ETSA-USJ/curso-3d-printing/Piezas Imprimibles/PrusaMendel_IT2_Usj/metric-prusa-lme8uu/ybrac-t.stl

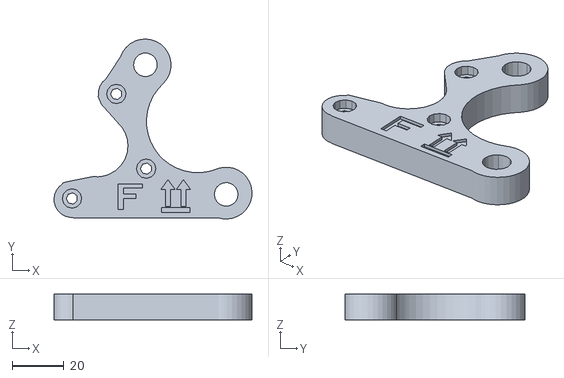
[picture p34: CAD file, 2014-04-24]
Piezas Imprimibles/PrusaMendel_IT2_Usj/metric-prusa-lme8uu/ybrac-t.stl
76.4 x 69.4 x 10.0
