ETSA-USJ/curso-3d-printing/Piezas Imprimibles/PrusaMendel_IT2_Usj/metric-prusa/printable-bushing-lm8uu.stl

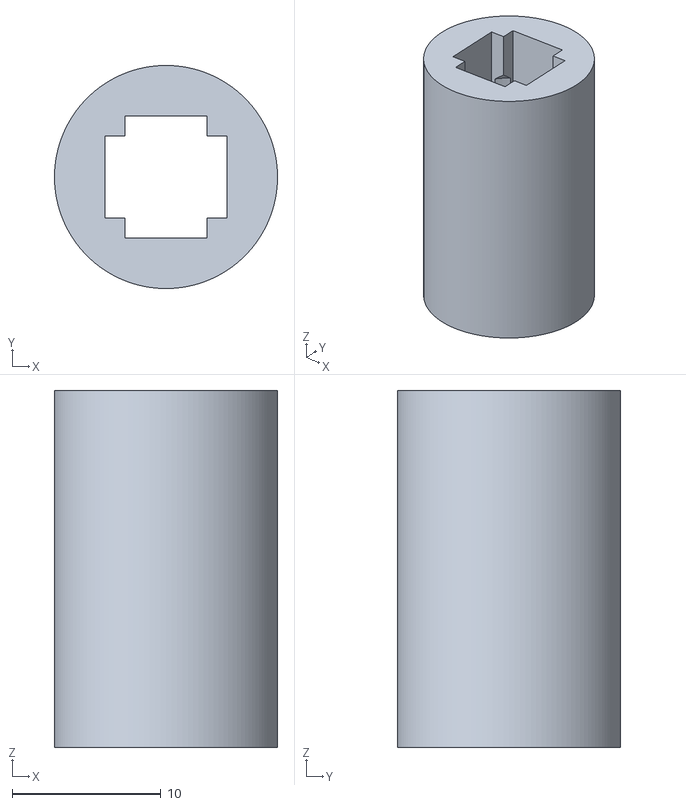
[picture p35: CAD file, 2014-04-24]
Piezas Imprimibles/PrusaMendel_IT2_Usj/metric-prusa/printable-bushing-lm8uu.stl
15.0 x 15.0 x 24.0
