ETSA-USJ/curso-3d-printing/Piezas Imprimibles/PrusaMendel_IT2_Usj/metric-prusa-lm8uu/frame-vertex.stl

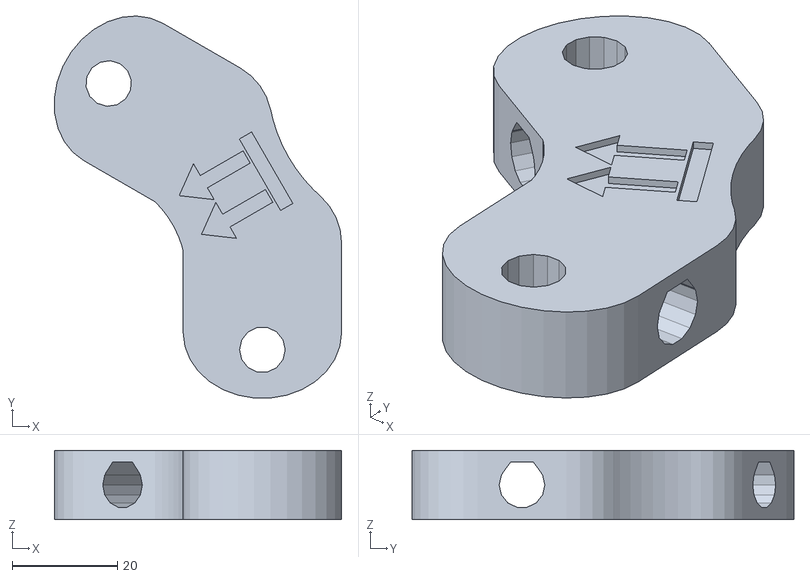
[picture p36: CAD file, 2014-04-24]
Piezas Imprimibles/PrusaMendel_IT2_Usj/metric-prusa-lm8uu/frame-vertex.stl
54.7 x 72.7 x 13.2
