ETSA-USJ/curso-3d-printing/Piezas Imprimibles/PrusaMendel_IT2_Usj/metric-prusa-lme8uu/frame-vertex-foot.stl

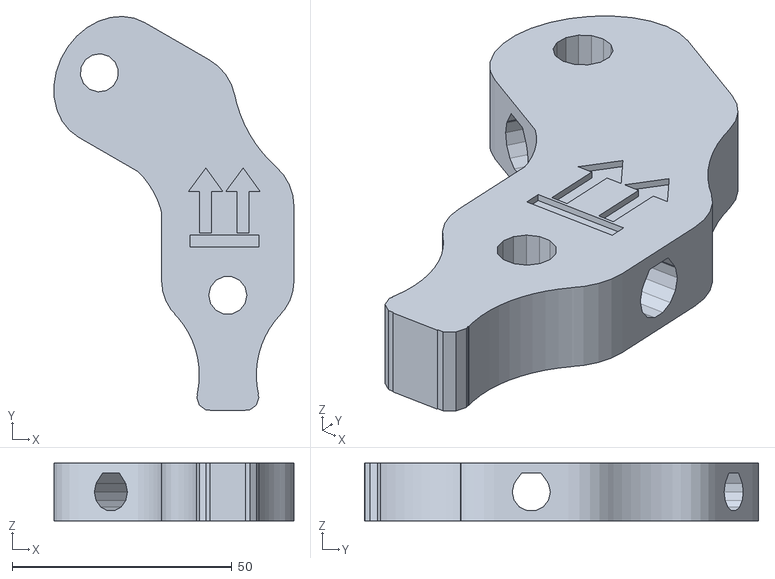
[picture p37: CAD file, 2014-04-24]
Piezas Imprimibles/PrusaMendel_IT2_Usj/metric-prusa-lme8uu/frame-vertex-foot.stl
54.7 x 89.8 x 13.2
