ETSA-USJ/curso-3d-printing/Piezas Imprimibles/PrusaMendel_IT2_Usj/metric-prusa-lm8uu/x-carriage.stl

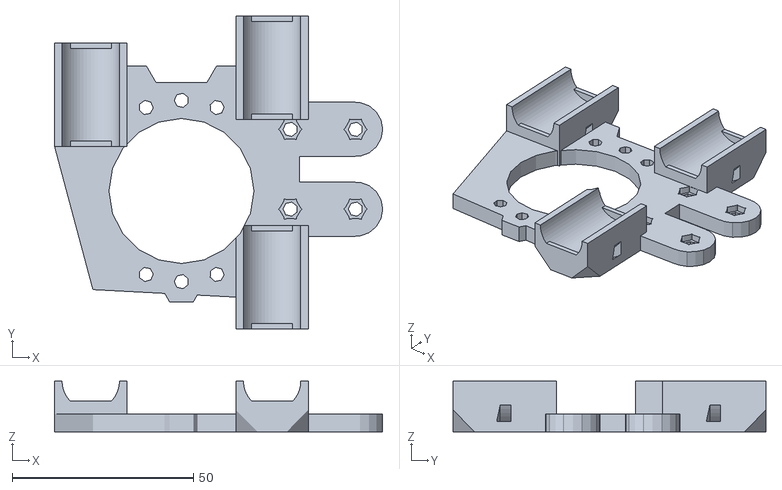
[picture p38: CAD file, 2014-04-24]
Piezas Imprimibles/PrusaMendel_IT2_Usj/metric-prusa-lm8uu/x-carriage.stl
90.6 x 86.3 x 14.0
