ETSA-USJ/curso-3d-printing/Piezas Imprimibles/PrusaMendel_IT2_Usj/metric-prusa-lme8uu/printable-bushing.stl

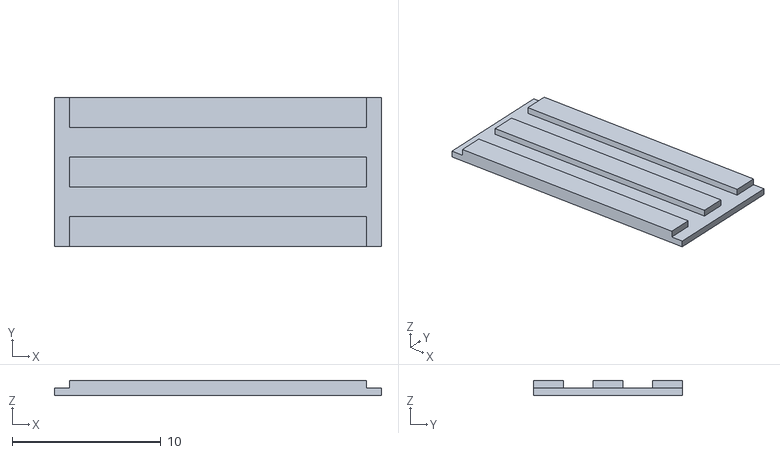
[picture p39: CAD file, 2014-04-24]
Piezas Imprimibles/PrusaMendel_IT2_Usj/metric-prusa-lme8uu/printable-bushing.stl
22.0 x 10.0 x 1.00
