ETSA-USJ/curso-3d-printing/Piezas Imprimibles/PrusaMendel_IT2_Usj/metric-prusa-lme8uu/x-end-motor.stl

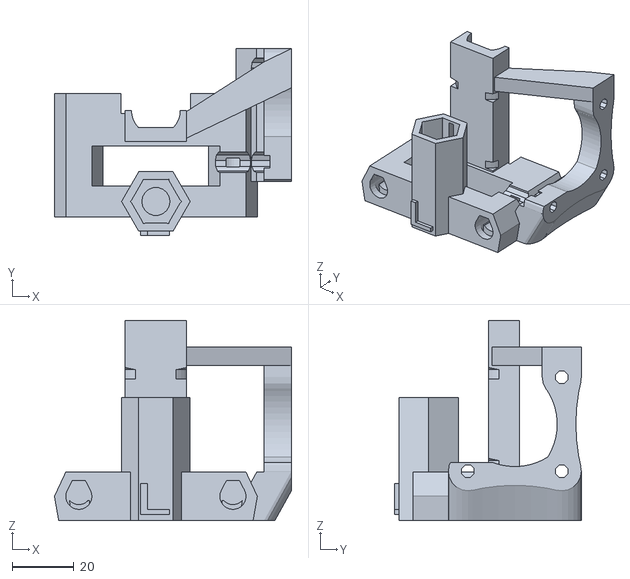
[picture p40: CAD file, 2014-04-24]
Piezas Imprimibles/PrusaMendel_IT2_Usj/metric-prusa-lme8uu/x-end-motor.stl
76.9 x 60.6 x 65.0
