ETSA-USJ/curso-3d-printing/Piezas Imprimibles/PrusaMendel_IT2_Usj/metric-prusa/rod-clamp.stl

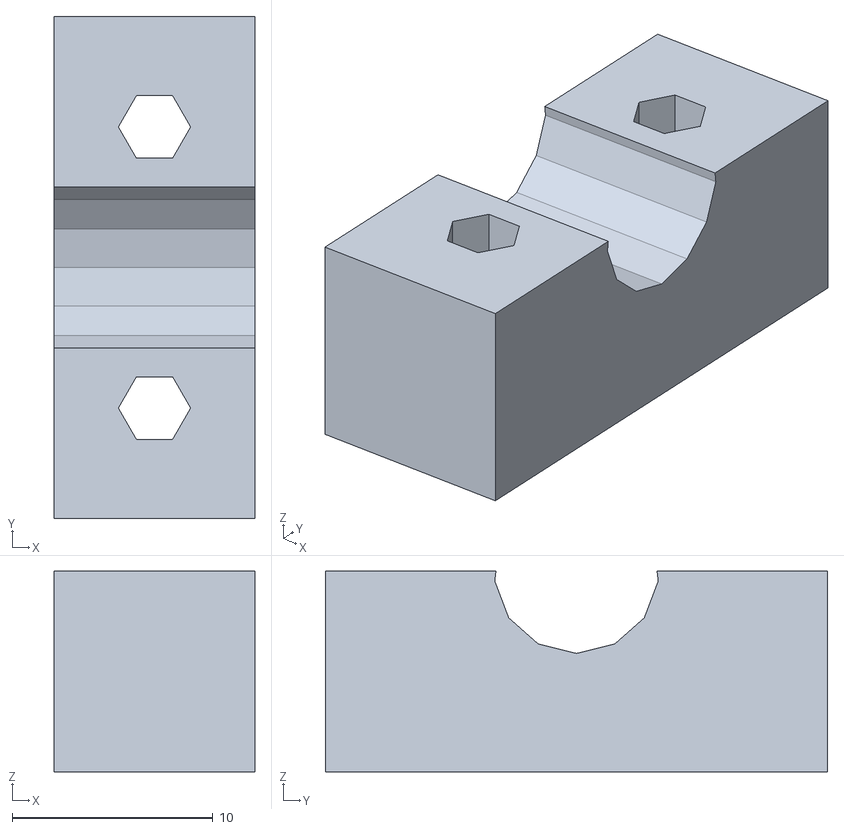
[picture p41: CAD file, 2014-04-24]
Piezas Imprimibles/PrusaMendel_IT2_Usj/metric-prusa/rod-clamp.stl
10.0 x 25.0 x 10.0
