ETSA-USJ/curso-3d-printing/Piezas Imprimibles/PrusaMendel_IT2_Usj/metric-prusa-lme8uu/endstop-holder.stl

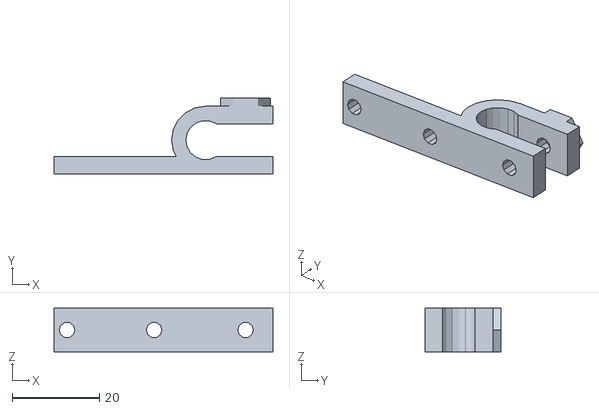
[picture p42: CAD file, 2014-04-24]
Piezas Imprimibles/PrusaMendel_IT2_Usj/metric-prusa-lme8uu/endstop-holder.stl
50.3 x 17.5 x 10.0
