ETSA-USJ/curso-3d-printing/Piezas Imprimibles/PrusaMendel_IT2_Usj/metric-prusa/mendel-plate-1.stl

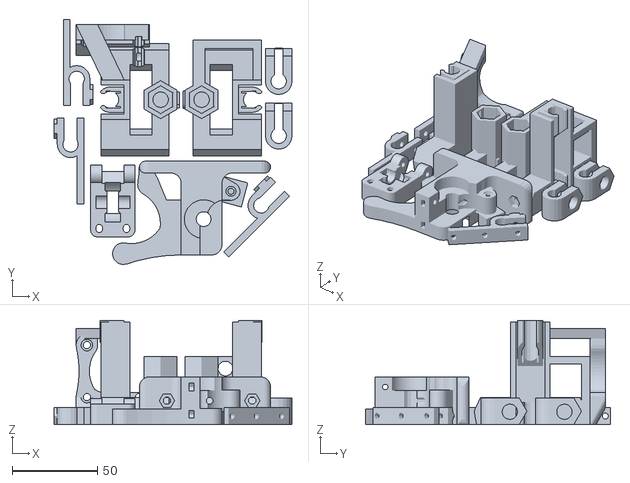
[picture p43: CAD file, 2014-04-24]
Piezas Imprimibles/PrusaMendel_IT2_Usj/metric-prusa/mendel-plate-1.stl
139.5 x 143.6 x 61.0
