ETSA-USJ/curso-3d-printing/Piezas Imprimibles/PrusaMendel_IT2_Usj/metric-prusa-lm8uu/sanguinololu-holder.stl

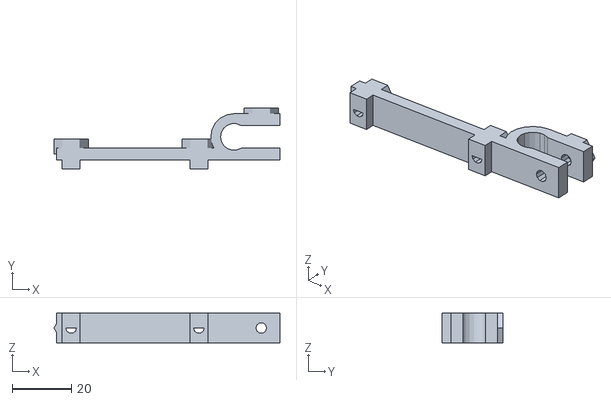
[picture p44: CAD file, 2014-04-24]
Piezas Imprimibles/PrusaMendel_IT2_Usj/metric-prusa-lm8uu/sanguinololu-holder.stl
76.1 x 20.5 x 10.0
