ETSA-USJ/curso-3d-printing/Piezas Imprimibles/PrusaMendel_IT2_Usj/metric-prusa/mendel-plate-2.stl

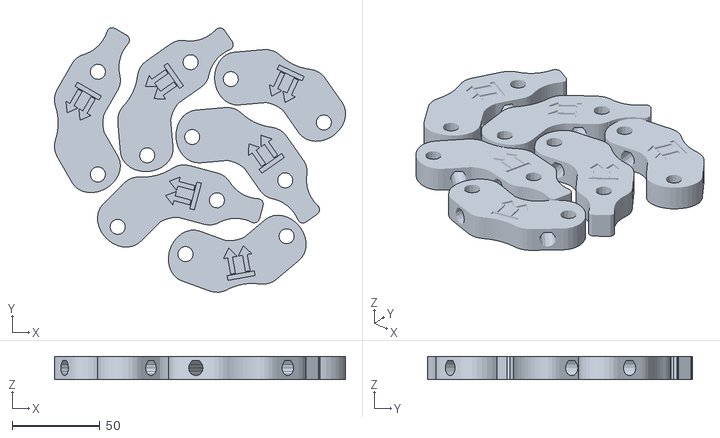
[picture p47: CAD file, 2014-04-24]
Piezas Imprimibles/PrusaMendel_IT2_Usj/metric-prusa/mendel-plate-2.stl
165.8 x 150.8 x 13.2
