ETSA-USJ/curso-3d-printing/Piezas Imprimibles/PrusaMendel_IT2_Usj/metric-prusa-lm8uu/bar-clamp.stl

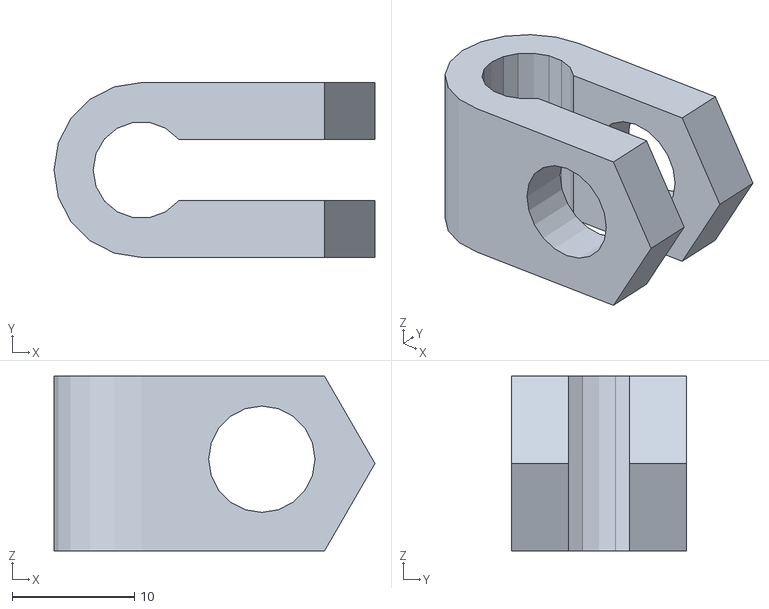
[picture p51: CAD file, 2014-04-24]
Piezas Imprimibles/PrusaMendel_IT2_Usj/metric-prusa-lm8uu/bar-clamp.stl
26.3 x 14.3 x 14.3
