ETSA-USJ/curso-3d-printing/Piezas Imprimibles/PrusaMendel_IT2_Usj/metric-prusa/mendel-plate-3.stl

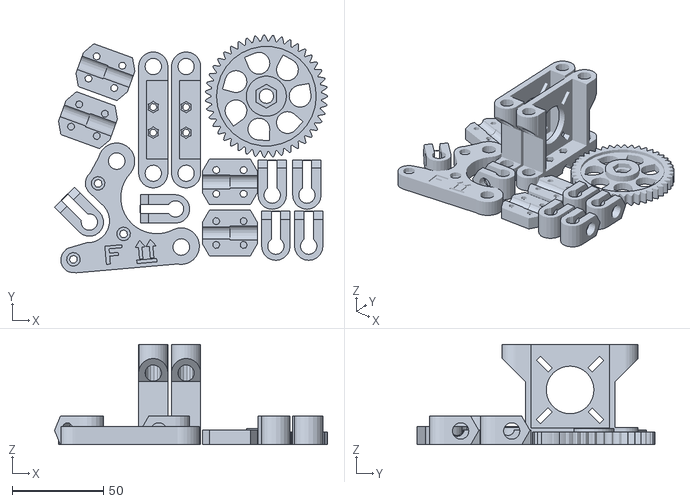
[picture p52: CAD file, 2014-04-24]
Piezas Imprimibles/PrusaMendel_IT2_Usj/metric-prusa/mendel-plate-3.stl
149.6 x 130.3 x 55.0
