ETSA-USJ/curso-3d-printing/Piezas Imprimibles/PrusaMendel_IT2_Usj/metric-prusa-lm8uu/mendel-plate-4.stl

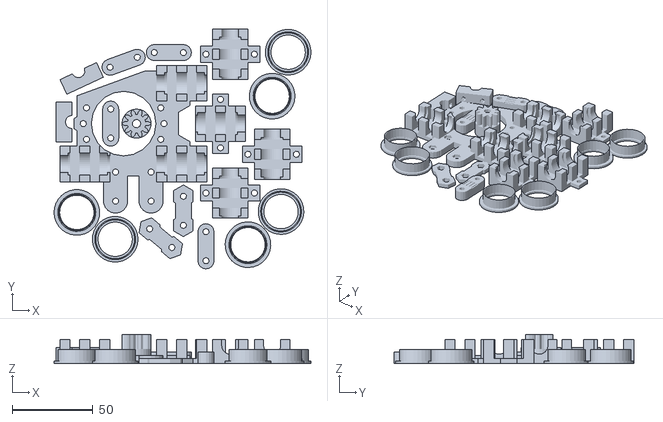
[picture p53: CAD file, 2014-04-24]
Piezas Imprimibles/PrusaMendel_IT2_Usj/metric-prusa-lm8uu/mendel-plate-4.stl
159.2 x 148.6 x 18.0
