ETSA-USJ/curso-3d-printing/Piezas Imprimibles/PrusaMendel_IT2_Usj/metric-prusa/experimental-extruder.stl

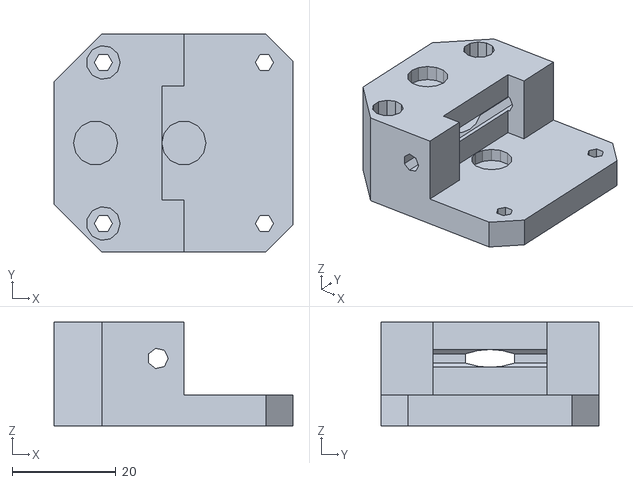
[picture p54: CAD file, 2014-04-24]
Piezas Imprimibles/PrusaMendel_IT2_Usj/metric-prusa/experimental-extruder.stl
46.0 x 42.0 x 20.0
