ETSA-USJ/curso-3d-printing/Software/Sprinter/R2D2_SF41_dot_skeinforge/profiles/extrusion/7-14-11-Retraction-test/chamber.csv

Format is tab separated chamber settings.
_Name | Value
WindowPosition | 700+0
Open File for Chamber
Activate Chamber: | False
Bed Temperature (Celcius): | 60.0
Chamber Temperature (Celcius): | 30.0
Holding Force (bar): | 0.0
