ETSA-USJ/curso-3d-printing/Software/Sprinter/R2D2_SF41_dot_skeinforge/profiles/extrusion/7-14-11-Retraction-test/chop.csv

Format is tab separated chop settings.
_Name | Value
WindowPosition | 600+0
Open File to be Chopped
Add Extra Top Layer if Necessary | True
Add Layer Template to SVG | True
Extra Decimal Places (float): | 2.0
Import Coarseness (ratio): | 1.0
Layer Thickness (mm): | 10.0
Layers From (index): | 0
Layers To (index): | 999999999
Correct Mesh | True
Unproven Mesh | False
Perimeter Width (mm): | 2.0
SVG Viewer: | webbrowser
