ETSA-USJ/curso-3d-printing/Software/Sprinter/R2D2_SF41_dot_skeinforge/profiles/extrusion/7-14-11-Retraction-test/clip.csv

Format is tab separated clip settings.
_Name | Value
WindowPosition | 700+0
Open File for Clip
Activate Clip | False
Clip Over Perimeter Width (ratio): | 0.5
Maximum Connection Distance Over Perimeter Width (ratio): | 10.0
