ETSA-USJ/curso-3d-printing/Software/Sprinter/R2D2_SF41_dot_skeinforge/profiles/extrusion/7-14-11-Retraction-test/comb.csv

Format is tab separated comb settings.
_Name | Value
WindowPosition | 700+0
Open File for Comb
Activate Comb | False
